hello42world/zigmo/Source/zcl_zigmo.c

/**************************************************************************************************
  Filename:       zcl_zigmo.c
  Revised:        $Date: 2015-08-19 17:11:00 -0700 (Wed, 19 Aug 2015) $
  Revision:       $Revision: 44460 $

  Description:    Zigbee Cluster Library - sample switch application.


  Copyright 2006-2013 Texas Instruments Incorporated. All rights reserved.

  IMPORTANT: Your use of this Software is limited to those specific rights
  granted under the terms of a software license agreement between the user
  who downloaded the software, his/her employer (which must be your employer)
  and Texas Instruments Incorporated (the "License").  You may not use this
  Software unless you agree to abide by the terms of the License. The License
  limits your use, and you acknowledge, that the Software may not be modified,
  copied or distributed unless embedded on a Texas Instruments microcontroller
  or used solely and exclusively in conjunction with a Texas Instruments radio
  frequency transceiver, which is integrated into your product.  Other than for
  the foregoing purpose, you may not use, reproduce, copy, prepare derivative
  works of, modify, distribute, perform, display or sell this Software and/or
  its documentation for any purpose.

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
  Should you have any questions regarding your right to use this Software,
  contact Texas Instruments Incorporated at www.TI.com.
**************************************************************************************************/

/*********************************************************************
  This application implements a ZigBee On/Off Switch, based on Z-Stack 3.0.

  This application is based on the common sample-application user interface. Please see the main
  comment in zcl_sampleapp_ui.c. The rest of this comment describes only the content specific for
  this sample applicetion.

  Application-specific UI peripherals being used:

  - none (LED1 is currently unused by this application).

  Application-specific menu system:

    <TOGGLE LIGHT> Send an On, Off or Toggle command targeting appropriate devices from the binding table.
      Pressing / releasing [OK] will have the following functionality, depending on the value of the
      zclZigmo_OnOffSwitchActions attribute:
      - OnOffSwitchActions == 0: pressing [OK] will send ON command, releasing it will send OFF command;
      - OnOffSwitchActions == 1: pressing [OK] will send OFF command, releasing it will send ON command;
      - OnOffSwitchActions == 2: pressing [OK] will send TOGGLE command, releasing it will not send any command.

*********************************************************************/

#if ! defined ZCL_ON_OFF
#error ZCL_ON_OFF must be defined for this project.
#endif

/*********************************************************************
 * INCLUDES
 */
#include "zcl_zigmo.h"


#include "ZComDef.h"
#include "OSAL.h"
#include "AF.h"
#include "ZDApp.h"
#include "ZDObject.h"
#include "ZDProfile.h"
#include "MT_SYS.h"

#include "zcl.h"
#include "zcl_general.h"
#include "zcl_ha.h"
#include "zcl_diagnostic.h"

#include "onboard.h"

/* HAL */
#include "hal2.h"
#include "hal_lcd.h"
#include "hal_led.h"
#include "hal_key.h"
#include "hal_adc.h"

#if defined (OTA_CLIENT) && (OTA_CLIENT == TRUE)
#include "zcl_ota.h"
#include "hal_ota.h"
#endif

#include "bdb.h"
#include "bdb_interface.h"

#include "DebugTrace.h"

#include "dbg.h"
#include "button.h"
#include "led.h"

STATIC_ASSERT(NWK_MAX_BINDING_ENTRIES == 5, we_have_5_endpoints_so_need_5_entries);


/*********************************************************************
 * MACROS
 */

#define APP_TITLE "Zigmo!"

/*********************************************************************
 * TYPEDEFS
 */

/*********************************************************************
 * GLOBAL VARIABLES
 */
byte zclZigmo_TaskID;
uint8 g_zigmo_battery_percentage;

#define ZIGMO_UPDATE_SENSORS_EVT   0x1000
/*********************************************************************
 * GLOBAL FUNCTIONS
 */

/*********************************************************************
 * LOCAL VARIABLES
 */
afAddrType_t zclZigmo_DstAddr;

// Endpoint to allow SYS_APP_MSGs
static endPointDesc_t zigmo_TestEp =
{
  ZIGMO_ENDPOINT,                  // endpoint
  0,
  &zclZigmo_TaskID,
  (SimpleDescriptionFormat_t *)NULL,  // No Simple description for this test endpoint
  (afNetworkLatencyReq_t)0            // No Network Latency req
};

devStates_t zclZigmo_NwkState = DEV_INIT;

#if defined (OTA_CLIENT) && (OTA_CLIENT == TRUE)
#define DEVICE_POLL_RATE                 8000   // Poll rate for end device
#endif

/*********************************************************************
 * LOCAL FUNCTIONS
 */
static void zclZigmo_BasicResetCB( void );

static void zclZigmo_ProcessCommissioningStatus(bdbCommissioningModeMsg_t *bdbCommissioningModeMsg);


// Functions to process ZCL Foundation incoming Command/Response messages
static void zclZigmo_ProcessIncomingMsg( zclIncomingMsg_t *msg );
#ifdef ZCL_READ
static uint8 zclZigmo_ProcessInReadRspCmd( zclIncomingMsg_t *pInMsg );
#endif
#ifdef ZCL_WRITE
static uint8 zclZigmo_ProcessInWriteRspCmd( zclIncomingMsg_t *pInMsg );
#endif
static uint8 zclZigmo_ProcessInDefaultRspCmd( zclIncomingMsg_t *pInMsg );
#ifdef ZCL_DISCOVER
static uint8 zclZigmo_ProcessInDiscCmdsRspCmd( zclIncomingMsg_t *pInMsg );
static uint8 zclZigmo_ProcessInDiscAttrsRspCmd( zclIncomingMsg_t *pInMsg );
static uint8 zclZigmo_ProcessInDiscAttrsExtRspCmd( zclIncomingMsg_t *pInMsg );
#endif

#if defined (OTA_CLIENT) && (OTA_CLIENT == TRUE)
static void zclZigmo_ProcessOTAMsgs( zclOTA_CallbackMsg_t* pMsg );
#endif


static void zclSampleApp_BatteryWarningCB( uint8 voltLevel);


/*********************************************************************
 * CONSTANTS
 */

/*********************************************************************
 * REFERENCED EXTERNALS
 */
extern int16 zdpExternalStateTaskID;

/*********************************************************************
 * ZCL General Profile Callback table
 */
static zclGeneral_AppCallbacks_t zclZigmo_CmdCallbacks =
{
  zclZigmo_BasicResetCB,               // Basic Cluster Reset command
  NULL,                                   // Identify Trigger Effect command
  NULL,                                   // On/Off cluster commands
  NULL,                                   // On/Off cluster enhanced command Off with Effect
  NULL,                                   // On/Off cluster enhanced command On with Recall Global Scene
  NULL,                                   // On/Off cluster enhanced command On with Timed Off
#ifdef ZCL_LEVEL_CTRL
  NULL,                                   // Level Control Move to Level command
  NULL,                                   // Level Control Move command
  NULL,                                   // Level Control Step command
  NULL,                                   // Level Control Stop command
#endif
#ifdef ZCL_GROUPS
  NULL,                                   // Group Response commands
#endif
#ifdef ZCL_SCENES
  NULL,                                   // Scene Store Request command
  NULL,                                   // Scene Recall Request command
  NULL,                                   // Scene Response command
#endif
#ifdef ZCL_ALARMS
  NULL,                                   // Alarm (Response) commands
#endif
#ifdef SE_UK_EXT
  NULL,                                   // Get Event Log command
  NULL,                                   // Publish Event Log command
#endif
  NULL,                                   // RSSI Location command
  NULL                                    // RSSI Location Response command
};


static void zigmo_init_battery_meter_pins(void)
{
  // Power pin
  // Set P1_5 to GPIO
  P1SEL &= ~(1 << 5);
  // Set P1_5 direction to Output.
  P1DIR |= (1 << 5);

  // ADC pin P0_6
  APCFG |= (1 << 6);
}

/*********************************************************************
 * @fn          zclZigmo_Init
 *
 * @brief       Initialization function for the zclGeneral layer.
 *
 * @param       none
 *
 * @return      none
 */
void zclZigmo_Init( byte task_id )
{
  zclZigmo_TaskID = task_id;


  // Set destination address to indirect
  zclZigmo_DstAddr.addrMode = (afAddrMode_t)AddrNotPresent;
  zclZigmo_DstAddr.endPoint = 0;
  zclZigmo_DstAddr.addr.shortAddr = 0;

  // Register the Simple Descriptor for this application
  bdb_RegisterSimpleDescriptor( &zclZigmo_SimpleDesc );

  // Register the ZCL General Cluster Library callback functions
  zclGeneral_RegisterCmdCallbacks( ZIGMO_ENDPOINT, &zclZigmo_CmdCallbacks );

  zclZigmo_ResetAttributesToDefaultValues();

  // Register the application's attribute list
  zcl_registerAttrList( ZIGMO_ENDPOINT, zclZigmo_NumAttributes, zclZigmo_Attrs );

  // Register the Application to receive the unprocessed Foundation command/response messages
  zcl_registerForMsg( zclZigmo_TaskID );

  // Register low voltage NV memory protection application callback
  RegisterVoltageWarningCB( zclSampleApp_BatteryWarningCB );

  bdb_RegisterCommissioningStatusCB( zclZigmo_ProcessCommissioningStatus );

  // Register for a test endpoint
  afRegister( &zigmo_TestEp );

#ifdef ZCL_DIAGNOSTIC
  // Register the application's callback function to read/write attribute data.
  // This is only required when the attribute data format is unknown to ZCL.
  zcl_registerReadWriteCB( ZIGMO_ENDPOINT, zclDiagnostic_ReadWriteAttrCB, NULL );

  if ( zclDiagnostic_InitStats() == ZSuccess )
  {
    // Here the user could start the timer to save Diagnostics to NV
  }
#endif

#if defined (OTA_CLIENT) && (OTA_CLIENT == TRUE)
  // Register for callback events from the ZCL OTA
  zclOTA_Register(zclZigmo_TaskID);
#endif

  zdpExternalStateTaskID = zclZigmo_TaskID;

  // Set transmission power
  ZMacSetTransmitPower(TX_PWR_PLUS_4);

  // Start timer
  osal_start_timerEx(zclZigmo_TaskID, ZIGMO_UPDATE_SENSORS_EVT, 5000);

  // Init buttons
  zigmo_buttons_set_target_task(zclZigmo_TaskID);

  // Init moisture sensors
  zigmo_moisture_sensor_init_sensors(
    ZIGMO_FIRST_SENSOR_ENDPOINT,
    &zclZigmo_CmdCallbacks);

  // Init battery percentage metering
  zigmo_init_battery_meter_pins();
  g_zigmo_battery_percentage = zigmo_get_battery_percentage();
  bdb_RepAddAttrCfgRecordDefaultToList(ZIGMO_ENDPOINT,
                 ZCL_CLUSTER_ID_GEN_POWER_CFG,
                 ATTRID_POWER_CFG_BATTERY_PERCENTAGE_REMAINING,
                 0, 10, reportableChange);

  // Rejoin the network. Should be the last step.
  bdb_StartCommissioning(BDB_COMMISSIONING_REJOIN_EXISTING_NETWORK_ON_STARTUP);
}

void zclZigmo_JoinNetwork(void)
{
  zgWriteStartupOptions( ZG_STARTUP_SET, ZCD_STARTOPT_DEFAULT_NETWORK_STATE | ZCD_STARTOPT_DEFAULT_CONFIG_STATE );

  // -DDEFAULT_CHANLIST=0x00000F00  // 11 - 0x0B
  // -DDEFAULT_CHANLIST=0x00008000  // 15 - 0x0F
  // -DDEFAULT_CHANLIST=0x00100000  // 20 - 0x14
  // -DDEFAULT_CHANLIST=0x02000000  // 25 - 0x19
  bdb_setChannelAttribute(true, 0x02108F00);
  bdb_setChannelAttribute(false, 0);
  bdb_StartCommissioning(BDB_COMMISSIONING_MODE_NWK_STEERING);
}

/**
* The return value here is percentage times 2.
* That is what ZCL expects.
*/
uint8 zigmo_get_battery_percentage(void)
{
  // adc 323 = 3.13v

  HalAdcSetReference(HAL_ADC_REF_125V);

  ZIGMO_VMETER_PWR_PIN = 1;
  zigmo_util_delay(2000);

  int32 adc;
  int32 ksave0 = 0;

  /* Keep on reading the ADC until two consecutive key decisions are the same. */
  do
  {
    ksave0 = adc;
    adc = HalAdcRead (HAL_ADC_CHN_AIN6, HAL_ADC_RESOLUTION_10);
  } while (adc != ksave0);

  ZIGMO_VMETER_PWR_PIN = 0;

  static const int32 adc_max = 400;
  static const int32 adc_min = 190;

  adc -= adc_min;
  if (adc < 0) adc = 0;
  adc = adc * 200 / (adc_max - adc_min);
  if (adc > 200) adc = 200;

  return adc;
}

/*********************************************************************
 * @fn          zclSample_event_loop
 *
 * @brief       Event Loop Processor for zclGeneral.
 *
 * @param       none
 *
 * @return      none
 */
uint16 zclZigmo_event_loop( uint8 task_id, uint16 events )
{
  afIncomingMSGPacket_t *MSGpkt;

  (void)task_id;  // Intentionally unreferenced parameter

  if (events & ZIGMO_UPDATE_SENSORS_EVT)
  {
    // Update every 5 minutes.
    osal_start_timerEx(zclZigmo_TaskID, ZIGMO_UPDATE_SENSORS_EVT, (uint32)5 * 60 * 1000);

    // Magic. Somehow UART freezes if we don't periodically read ADC.
    // HalAdcRead (HAL_ADC_CHN_AIN4, HAL_ADC_RESOLUTION_10);

    if (bdbAttributes.bdbNodeIsOnANetwork == TRUE)
    {
      g_zigmo_battery_percentage = zigmo_get_battery_percentage();
      bdb_RepChangedAttrValue(
        ZIGMO_ENDPOINT,
        ZCL_CLUSTER_ID_GEN_POWER_CFG,
        ATTRID_POWER_CFG_BATTERY_PERCENTAGE_REMAINING);

      zigmo_led_on();
      zigmo_moisture_sensors_refresh(ZIGMO_FIRST_SENSOR_ENDPOINT);
      zigmo_led_off();
    }

    // return unprocessed events
    return (events ^ ZIGMO_UPDATE_SENSORS_EVT);
  }


  if ( events & SYS_EVENT_MSG )
  {
    while ( (MSGpkt = (afIncomingMSGPacket_t *)osal_msg_receive( zclZigmo_TaskID )) )
    {
      switch ( MSGpkt->hdr.event )
      {
        case ZCL_INCOMING_MSG:
          // Incoming ZCL Foundation command/response messages
          zclZigmo_ProcessIncomingMsg( (zclIncomingMsg_t *)MSGpkt );
          break;

        case ZIGMO_BTN_EVENT:
          if (bdbAttributes.bdbCommissioningStatus != BDB_COMMISSIONING_IN_PROGRESS)
          {
            zigmo_led_blink(2);
            zclZigmo_JoinNetwork();
          }
          break;

#if defined (OTA_CLIENT) && (OTA_CLIENT == TRUE)
        case ZCL_OTA_CALLBACK_IND:
          zclZigmo_ProcessOTAMsgs( (zclOTA_CallbackMsg_t*)MSGpkt  );
          break;
#endif

        default:
          break;
      }

      // Release the memory
      osal_msg_deallocate( (uint8 *)MSGpkt );
    }

    // return unprocessed events
    return (events ^ SYS_EVENT_MSG);
  }

#if ZG_BUILD_ENDDEVICE_TYPE
  if ( events & SAMPLEAPP_END_DEVICE_REJOIN_EVT )
  {
    bdb_ZedAttemptRecoverNwk();
    return ( events ^ SAMPLEAPP_END_DEVICE_REJOIN_EVT );
  }
#endif

  // Discard unknown events
  return 0;
}


/*********************************************************************
 * @fn      zclZigmo_ProcessCommissioningStatus
 *
 * @brief   Callback in which the status of the commissioning process are reported
 *
 * @param   bdbCommissioningModeMsg - Context message of the status of a commissioning process
 *
 * @return  none
 */
static void zclZigmo_ProcessCommissioningStatus(bdbCommissioningModeMsg_t *bdbCommissioningModeMsg)
{
  switch(bdbCommissioningModeMsg->bdbCommissioningMode)
  {
    case BDB_COMMISSIONING_FORMATION:
      if(bdbCommissioningModeMsg->bdbCommissioningStatus == BDB_COMMISSIONING_SUCCESS)
      {
        //After formation, perform nwk steering again plus the remaining commissioning modes that has not been processed yet
        bdb_StartCommissioning(BDB_COMMISSIONING_MODE_NWK_STEERING | bdbCommissioningModeMsg->bdbRemainingCommissioningModes);
      }
      else
      {
        //Want to try other channels?
        //try with bdb_setChannelAttribute
      }
    break;
    case BDB_COMMISSIONING_NWK_STEERING:
      if(bdbCommissioningModeMsg->bdbCommissioningStatus == BDB_COMMISSIONING_SUCCESS)
      {
        //YOUR JOB:
        //We are on the nwk, what now?
      }
      else
      {
        //See the possible errors for nwk steering procedure
        //No suitable networks found
        //Want to try other channels?
        //try with bdb_setChannelAttribute
      }
    break;
    case BDB_COMMISSIONING_FINDING_BINDING:
      if(bdbCommissioningModeMsg->bdbCommissioningStatus == BDB_COMMISSIONING_SUCCESS)
      {
        //YOUR JOB:
      }
      else
      {
        //YOUR JOB:
        //retry?, wait for user interaction?
      }
    break;
    case BDB_COMMISSIONING_INITIALIZATION:
      //Initialization notification can only be successful. Failure on initialization
      //only happens for ZED and is notified as BDB_COMMISSIONING_PARENT_LOST notification

      //YOUR JOB:
      //We are on a network, what now?

    break;
#if ZG_BUILD_ENDDEVICE_TYPE
    case BDB_COMMISSIONING_PARENT_LOST:
      if(bdbCommissioningModeMsg->bdbCommissioningStatus == BDB_COMMISSIONING_NETWORK_RESTORED)
      {
        //We did recover from losing parent
      }
      else
      {
        //Parent not found, attempt to rejoin again after a fixed delay
        osal_start_timerEx(zclZigmo_TaskID, SAMPLEAPP_END_DEVICE_REJOIN_EVT, SAMPLEAPP_END_DEVICE_REJOIN_DELAY);
      }
    break;
#endif
  }
}

/*********************************************************************
 * @fn      zclZigmo_BasicResetCB
 *
 * @brief   Callback from the ZCL General Cluster Library
 *          to set all the Basic Cluster attributes to  default values.
 *
 * @param   none
 *
 * @return  none
 */
static void zclZigmo_BasicResetCB( void )
{
  zclZigmo_ResetAttributesToDefaultValues();
}

/*********************************************************************
 * @fn      zclSampleApp_BatteryWarningCB
 *
 * @brief   Called to handle battery-low situation.
 *
 * @param   voltLevel - level of severity
 *
 * @return  none
 */
void zclSampleApp_BatteryWarningCB( uint8 voltLevel )
{
  if ( voltLevel == VOLT_LEVEL_CAUTIOUS )
  {
    // Send warning message to the gateway and blink LED
  }
  else if ( voltLevel == VOLT_LEVEL_BAD )
  {
    // Shut down the system
  }
}

/******************************************************************************
 *
 *  Functions for processing ZCL Foundation incoming Command/Response messages
 *
 *****************************************************************************/

/*********************************************************************
 * @fn      zclZigmo_ProcessIncomingMsg
 *
 * @brief   Process ZCL Foundation incoming message
 *
 * @param   pInMsg - pointer to the received message
 *
 * @return  none
 */
static void zclZigmo_ProcessIncomingMsg( zclIncomingMsg_t *pInMsg )
{
  switch ( pInMsg->zclHdr.commandID )
  {
#ifdef ZCL_READ
    case ZCL_CMD_READ_RSP:
      zclZigmo_ProcessInReadRspCmd( pInMsg );
      break;
#endif
#ifdef ZCL_WRITE
    case ZCL_CMD_WRITE_RSP:
      zclZigmo_ProcessInWriteRspCmd( pInMsg );
      break;
#endif
#ifdef ZCL_REPORT
    // See ZCL Test Applicaiton (zcl_testapp.c) for sample code on Attribute Reporting
    case ZCL_CMD_CONFIG_REPORT:
      //zclZigmo_ProcessInConfigReportCmd( pInMsg );
      break;

    case ZCL_CMD_CONFIG_REPORT_RSP:
      //zclZigmo_ProcessInConfigReportRspCmd( pInMsg );
      break;

    case ZCL_CMD_READ_REPORT_CFG:
      //zclZigmo_ProcessInReadReportCfgCmd( pInMsg );
      break;

    case ZCL_CMD_READ_REPORT_CFG_RSP:
      //zclZigmo_ProcessInReadReportCfgRspCmd( pInMsg );
      break;

    case ZCL_CMD_REPORT:
      //zclZigmo_ProcessInReportCmd( pInMsg );
      break;
#endif
    case ZCL_CMD_DEFAULT_RSP:
      zclZigmo_ProcessInDefaultRspCmd( pInMsg );
      break;
#ifdef ZCL_DISCOVER
    case ZCL_CMD_DISCOVER_CMDS_RECEIVED_RSP:
      zclZigmo_ProcessInDiscCmdsRspCmd( pInMsg );
      break;

    case ZCL_CMD_DISCOVER_CMDS_GEN_RSP:
      zclZigmo_ProcessInDiscCmdsRspCmd( pInMsg );
      break;

    case ZCL_CMD_DISCOVER_ATTRS_RSP:
      zclZigmo_ProcessInDiscAttrsRspCmd( pInMsg );
      break;

    case ZCL_CMD_DISCOVER_ATTRS_EXT_RSP:
      zclZigmo_ProcessInDiscAttrsExtRspCmd( pInMsg );
      break;
#endif
    default:
      break;
  }

  if ( pInMsg->attrCmd )
    osal_mem_free( pInMsg->attrCmd );
}

#ifdef ZCL_READ
/*********************************************************************
 * @fn      zclZigmo_ProcessInReadRspCmd
 *
 * @brief   Process the "Profile" Read Response Command
 *
 * @param   pInMsg - incoming message to process
 *
 * @return  none
 */
static uint8 zclZigmo_ProcessInReadRspCmd( zclIncomingMsg_t *pInMsg )
{
  zclReadRspCmd_t *readRspCmd;
  uint8 i;

  readRspCmd = (zclReadRspCmd_t *)pInMsg->attrCmd;
  for (i = 0; i < readRspCmd->numAttr; i++)
  {
    // Notify the originator of the results of the original read attributes
    // attempt and, for each successfull request, the value of the requested
    // attribute
  }

  return TRUE;
}
#endif // ZCL_READ

#ifdef ZCL_WRITE
/*********************************************************************
 * @fn      zclZigmo_ProcessInWriteRspCmd
 *
 * @brief   Process the "Profile" Write Response Command
 *
 * @param   pInMsg - incoming message to process
 *
 * @return  none
 */
static uint8 zclZigmo_ProcessInWriteRspCmd( zclIncomingMsg_t *pInMsg )
{
  zclWriteRspCmd_t *writeRspCmd;
  uint8 i;

  writeRspCmd = (zclWriteRspCmd_t *)pInMsg->attrCmd;
  for (i = 0; i < writeRspCmd->numAttr; i++)
  {
    // Notify the device of the results of the its original write attributes
    // command.
  }

  return TRUE;
}
#endif // ZCL_WRITE

/*********************************************************************
 * @fn      zclZigmo_ProcessInDefaultRspCmd
 *
 * @brief   Process the "Profile" Default Response Command
 *
 * @param   pInMsg - incoming message to process
 *
 * @return  none
 */
static uint8 zclZigmo_ProcessInDefaultRspCmd( zclIncomingMsg_t *pInMsg )
{
  // zclDefaultRspCmd_t *defaultRspCmd = (zclDefaultRspCmd_t *)pInMsg->attrCmd;
  // Device is notified of the Default Response command.
  (void)pInMsg;
  return TRUE;
}

#ifdef ZCL_DISCOVER
/*********************************************************************
 * @fn      zclZigmo_ProcessInDiscCmdsRspCmd
 *
 * @brief   Process the Discover Commands Response Command
 *
 * @param   pInMsg - incoming message to process
 *
 * @return  none
 */
static uint8 zclZigmo_ProcessInDiscCmdsRspCmd( zclIncomingMsg_t *pInMsg )
{
  zclDiscoverCmdsCmdRsp_t *discoverRspCmd;
  uint8 i;

  discoverRspCmd = (zclDiscoverCmdsCmdRsp_t *)pInMsg->attrCmd;
  for ( i = 0; i < discoverRspCmd->numCmd; i++ )
  {
    // Device is notified of the result of its attribute discovery command.
  }

  return TRUE;
}

/*********************************************************************
 * @fn      zclZigmo_ProcessInDiscAttrsRspCmd
 *
 * @brief   Process the "Profile" Discover Attributes Response Command
 *
 * @param   pInMsg - incoming message to process
 *
 * @return  none
 */
static uint8 zclZigmo_ProcessInDiscAttrsRspCmd( zclIncomingMsg_t *pInMsg )
{
  zclDiscoverAttrsRspCmd_t *discoverRspCmd;
  uint8 i;

  discoverRspCmd = (zclDiscoverAttrsRspCmd_t *)pInMsg->attrCmd;
  for ( i = 0; i < discoverRspCmd->numAttr; i++ )
  {
    // Device is notified of the result of its attribute discovery command.
  }

  return TRUE;
}

/*********************************************************************
 * @fn      zclZigmo_ProcessInDiscAttrsExtRspCmd
 *
 * @brief   Process the "Profile" Discover Attributes Extended Response Command
 *
 * @param   pInMsg - incoming message to process
 *
 * @return  none
 */
static uint8 zclZigmo_ProcessInDiscAttrsExtRspCmd( zclIncomingMsg_t *pInMsg )
{
  zclDiscoverAttrsExtRsp_t *discoverRspCmd;
  uint8 i;

  discoverRspCmd = (zclDiscoverAttrsExtRsp_t *)pInMsg->attrCmd;
  for ( i = 0; i < discoverRspCmd->numAttr; i++ )
  {
    // Device is notified of the result of its attribute discovery command.
  }

  return TRUE;
}
#endif // ZCL_DISCOVER

#if defined (OTA_CLIENT) && (OTA_CLIENT == TRUE)
/*********************************************************************
 * @fn      zclZigmo_ProcessOTAMsgs
 *
 * @brief   Called to process callbacks from the ZCL OTA.
 *
 * @param   none
 *
 * @return  none
 */
static void zclZigmo_ProcessOTAMsgs( zclOTA_CallbackMsg_t* pMsg )
{
  uint8 RxOnIdle;

  switch(pMsg->ota_event)
  {
  case ZCL_OTA_START_CALLBACK:
    if (pMsg->hdr.status == ZSuccess)
    {
      // Speed up the poll rate
      RxOnIdle = TRUE;
      ZMacSetReq( ZMacRxOnIdle, &RxOnIdle );
      NLME_SetPollRate( 2000 );
    }
    break;

  case ZCL_OTA_DL_COMPLETE_CALLBACK:
    if (pMsg->hdr.status == ZSuccess)
    {
      // Reset the CRC Shadow and reboot.  The bootloader will see the
      // CRC shadow has been cleared and switch to the new image
      HalOTAInvRC();
      SystemReset();
    }
    else
    {
#if (ZG_BUILD_ENDDEVICE_TYPE)
      // slow the poll rate back down.
      RxOnIdle = FALSE;
      ZMacSetReq( ZMacRxOnIdle, &RxOnIdle );
      NLME_SetPollRate(DEVICE_POLL_RATE);
#endif
    }
    break;

  default:
    break;
  }
}
#endif // defined (OTA_CLIENT) && (OTA_CLIENT == TRUE)
